David-EIPI/stm32-weather-sensor/pcb/weather_sensor.kicad_sch

## KiCad design pcb/weather_sensor.kicad_sch (2025-03-25)

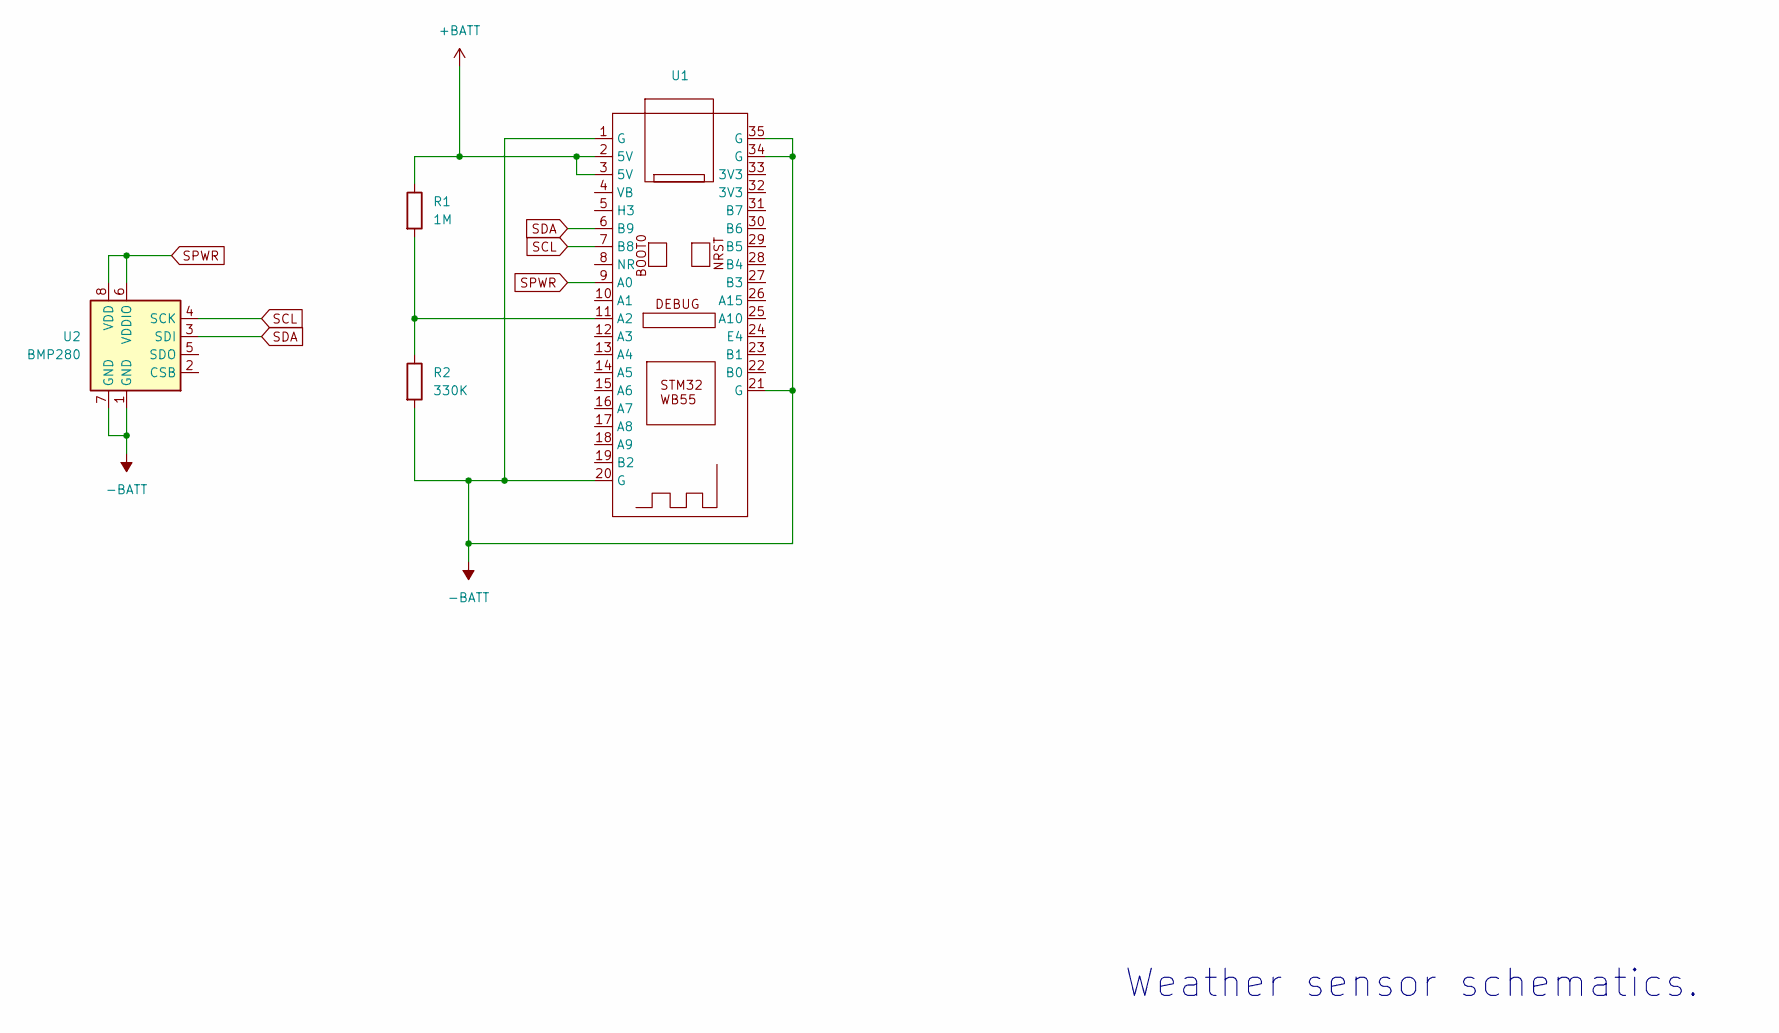
[picture p3: schematic weather_sensor.kicad_sch]

Parts:
R1: 1M
R2: 330K
U1: (no value)
U2: BMP280; Bosch_LGA-8_2x2.5mm_P0.65mm_ClockwisePinNumbering

Connections:
+BATT: R1.1, U1.2 (5V), U1.3 (5V)
-BATT: R2.2, U1.1 (G), U1.20 (G), U1.21 (G), U1.34 (G), U1.35 (G), U2.1 (GND), U2.7 (GND)
unnamed: R1.2, R2.1, U1.11 (A2)
SCL: U1.7 (B8), U2.4 (SCK)
SDA: U1.6 (B9), U2.3 (SDI)
SPWR: U1.9 (A0), U2.6 (VDDIO), U2.8 (VDD)

Notes on the sheet:
Weather sensor schematics.
