David-EIPI/stm32-weather-sensor/firmware/Core/Inc/main.h

#define BME280_Supply_Pin LL_GPIO_PIN_0
#define BME280_Supply_GPIO_Port GPIOA
#define BOARDLED_Pin LL_GPIO_PIN_4
#define BOARDLED_GPIO_Port GPIOE
